psrobotics/quadruped_bai_tiny/pic/20210320_233546.jpg

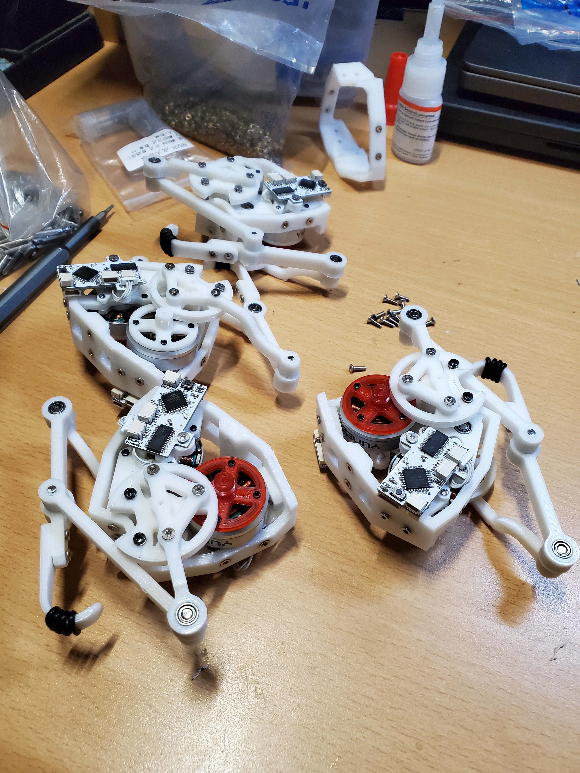
pic/20210320_233546.jpg
