psrobotics/quadruped_bai_tiny/pic/20210321_001258.jpg

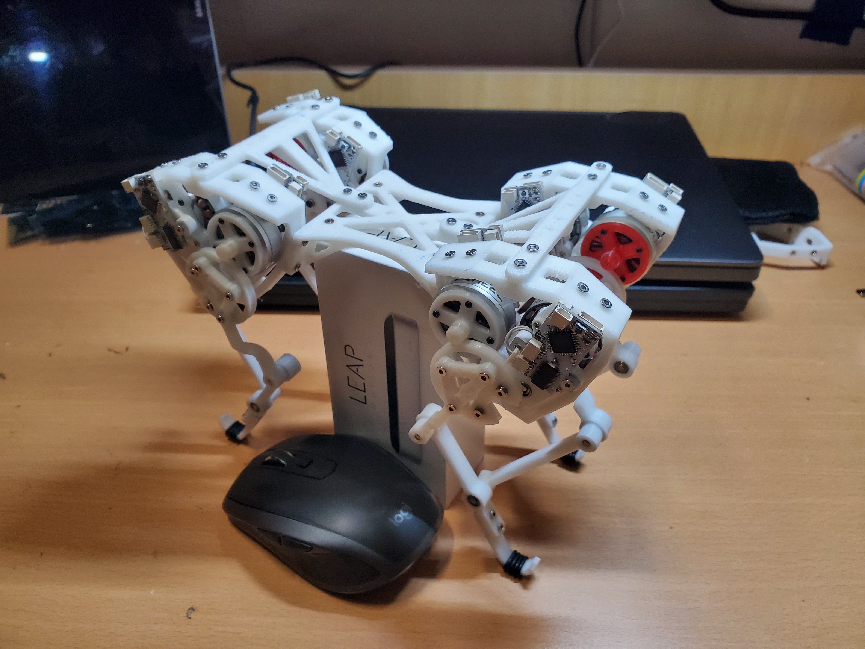
pic/20210321_001258.jpg
