psrobotics/quadruped_bai_tiny/software/ctr_1/main_m5_ctr/quick_math.h

#ifndef __QUICK_MATH_H_
#define __QUICK_MATH_H_

const float l1 = 29.1;
const float l2 = 48;
const float l3 = 38;
const float l6 = 34.5;
const float l5 = 33;
const float l4 = 60;

const float multiplier = 81.4873308631f;
const float pi = 3.14159265358979323846;

const float sin_table[] = {
  0, 0.012296, 0.024589, 0.036879, 0.049164, 0.061441, 0.073708, 0.085965, 0.098208, 0.11044, 0.12265, 0.13484, 0.14702, 0.15917, 0.17129, 0.18339, 0.19547, 0.20751, 0.21952, 0.2315, 0.24345, 0.25535, 0.26722, 0.27905, 0.29084, 0.30258, 0.31427, 0.32592, 0.33752, 0.34907, 0.36057, 0.37201, 0.38339, 0.39472, 0.40599, 0.41719, 0.42834, 0.43941, 0.45043, 0.46137, 0.47224, 0.48305, 0.49378, 0.50443, 0.51501, 0.52551, 0.53593, 0.54627, 0.55653, 0.5667, 0.57679, 0.58679, 0.5967, 0.60652, 0.61625, 0.62589, 0.63543, 0.64488, 0.65423, 0.66348, 0.67263, 0.68167, 0.69062, 0.69946, 0.70819, 0.71682, 0.72534, 0.73375, 0.74205, 0.75023, 0.75831, 0.76626, 0.77411, 0.78183, 0.78944, 0.79693, 0.80429, 0.81154, 0.81866, 0.82566, 0.83254, 0.83928, 0.84591, 0.8524, 0.85876, 0.865, 0.8711, 0.87708, 0.88292, 0.88862, 0.89419, 0.89963, 0.90493, 0.9101, 0.91512, 0.92001, 0.92476, 0.92937, 0.93384, 0.93816, 0.94235, 0.94639, 0.95029, 0.95405, 0.95766, 0.96113, 0.96445, 0.96763, 0.97066, 0.97354, 0.97628, 0.97887, 0.98131, 0.9836, 0.98574, 0.98774, 0.98958, 0.99128, 0.99282, 0.99422, 0.99546, 0.99656, 0.9975, 0.99829, 0.99894, 0.99943, 0.99977, 0.99996, 1, 0.99988, 0.99962, 0.9992, 0.99863, 0.99792, 0.99705, 0.99603, 0.99486, 0.99354, 0.99207, 0.99045, 0.98868, 0.98676, 0.98469, 0.98247, 0.9801, 0.97759, 0.97493, 0.97212, 0.96916, 0.96606, 0.96281, 0.95941, 0.95587, 0.95219, 0.94836, 0.94439, 0.94028, 0.93602, 0.93162, 0.92708, 0.9224, 0.91758, 0.91263, 0.90753, 0.9023, 0.89693, 0.89142, 0.88579, 0.88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
};

float quick_sin(float theta);
float quick_cos(float theta);

#endif
